MohamadAminGhanoum/IMU-board/IMU board assets/Screenshot 2026-07-07 at 11.47.00.png

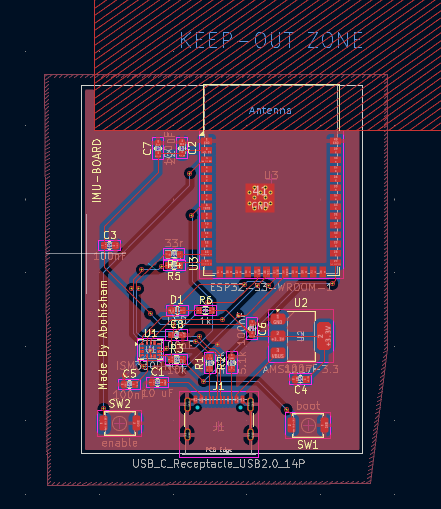
IMU board assets/Screenshot 2026-07-07 at 11.47.00.png
